majsterklepka/upgraded-system/software/multi-channel-voltmeter/dest.h

/*
 * @file dest.h
 *
 * @author Paweł Sobótka
 * @date 2020-06-12
 * @license GNU GPLv3
 *
 */

#pragma once

#ifndef _DEST_H_
#define _DEST_H_

int prefix(const char *data);
float suffix(const char *data);

#endif// _DEST_H_
